ntua-el20199/PLL/simulations/pll.asc

C1: cap; {C1}
C2: cap; {C2}
C3: cap; {10*C1}
D1: diode; 1N4148
D2: diode; 1N4148
D3: diode; 1N4148
D4: diode; 1N4148
Q1: npn; 2N2222
Q2: pnp; 2N2907
R1: res; 33K
R2: res; 47K
R3: res; 47K
R4: res; 33K
R5: res; 33K
R11: res; {2*R}
R12: res; {R}
R13: res; {R}
R14: res; {R}
U1: 74hct00
U2: 74hct00
U3: 74hct00
U4: 74hct74
U5: 74hct74
U6: LM324
U8: LM324
U9: 74hct74
U10: 74hct74
U11: sw_3_to_1; SEL={POS}
U12: 74hct14
U19: BS170
V2: voltage; 5
V3: voltage; PULSE(0 5 0 100p 100p {1/2/freq} {1/freq})
Named nets: 0, Vcc, Uin, OUT, Vcontrol
.tran 0.2
.include LM324.lib
.include BS170.lib
.include 74hct.lib
.include sw_3_to_1.sub
.meas TRAN tperiod TRIG V(OUT)=2.5 TD=180ms RISE=1 TARG V(OUT)=2.5 TD=180ms RISE=2
 
.meas TRAN FREQ PARAM 1/tperiod
.param POS 3
.step param POS list 1 2 3
.param freq 20K
.param R 27K
.param C2 1n
.param C1 47n
