ntua-el20199/PLL/simulations/vco.asc

C2: cap; {C}
M1: nmos
R12: res; {R2}
R13: res; {R}
R14: res; {R}
R15: res; {R}
U1: UniversalOpAmp2
U2: 74hct14
V1: voltage; {Vcontrol}
V2: voltage; 5
Named nets: 0, Vcc, Vctrl, OUT, Vd
.include LM324.lib
.include BS170.lib
.include 74HCT.lib
.tran 0 5m 0 100n
.step param R list 5K 10K 20K 40K 50K
.step param C list 0.001p 0.0001p 0.00001p
.step param Rst list 40K 56K 80K 100K 150K 200K
.meas TRAN tperiod TRIGV(out)=2.5 TD=3ms RISE=1 TARG V(out)=2.5 TD=3ms RISE=2
.meas TRAN FREQ PARAM 1/tperiod
.param Rst 20K
.param R 20K
.param R2 2*R
.param C 1pF
.param Vcontrol 5V
.option noopiter
