ntua-el20199/PLL/simulations/small_signal.asc

C1: cap; 0.1n
E3: e; Laplace={KVCO}/s; cache=2
E_ADDER: e; 1
E_DIVIDER: e; Laplace=1/{M}
E_PD: e; {KPD}
R1: res; 1K
V1: voltage; ""; AC 1
Named nets: phi_in, 0, phi_out
.param KPD=100 KVCO=1e3 M=10
Loop Filter
.ac dec 20 1 100MEG
VCO
PD
Divider
