ntua-el20199/PLL/simulations/simulation_log/pll_ideal.asc

C1: cap; 47n
C2: cap; 1n
C3: cap; 470n
D1: diode; 1N4148
D2: diode; 1N4148
D3: diode; 1N4148
D4: diode; 1N4148
M1: nmos
Q1: npn
Q2: pnp
R1: res; 33K
R2: res; 47K
R3: res; 47K
R4: res; 33K
R5: res; 33K
R8: res; 100K
R9: res; 100K
R10: res; 100K
R11: res; 56K
R12: res; 27K
R13: res; 27K
R14: res; 27K
U1: 74hct00
U2: 74hct00
U3: 74hct00
U4: 74hct74
U5: UniversalOpAmp2
U6: UniversalOpAmp2
U8: 74hct74
U9: 74hct74
U10: 74hct74
U11: UniversalOpAmp2
U12: 74hct14
V1: voltage; 5
V2: voltage; 5
V3: voltage; PULSE(0 5 0 1u 1u 50u 100u)
Named nets: 0, Vcc, Uin, Uout, Vcontrol, Vdd
.include 74hct.lib
.tran 0.5
.include LM324.lib
.include BS170.lib
